swapdisk/fpctl/3d/flaps-knob-pull-lower-pt2.scad

$fn=180;
eps=0.01;

difference() { 
    rotate([0, 0, 90]) translate([0, 0, 16.794-16.794]) {
            include <flaps-knob-pull-scaled.scad>;
    }
    translate([-49, -49, 1.793]) cube(99);
    
}
